Aryan-Kodan/Multi_Channel_DSO/images/KiCad/PCB.png

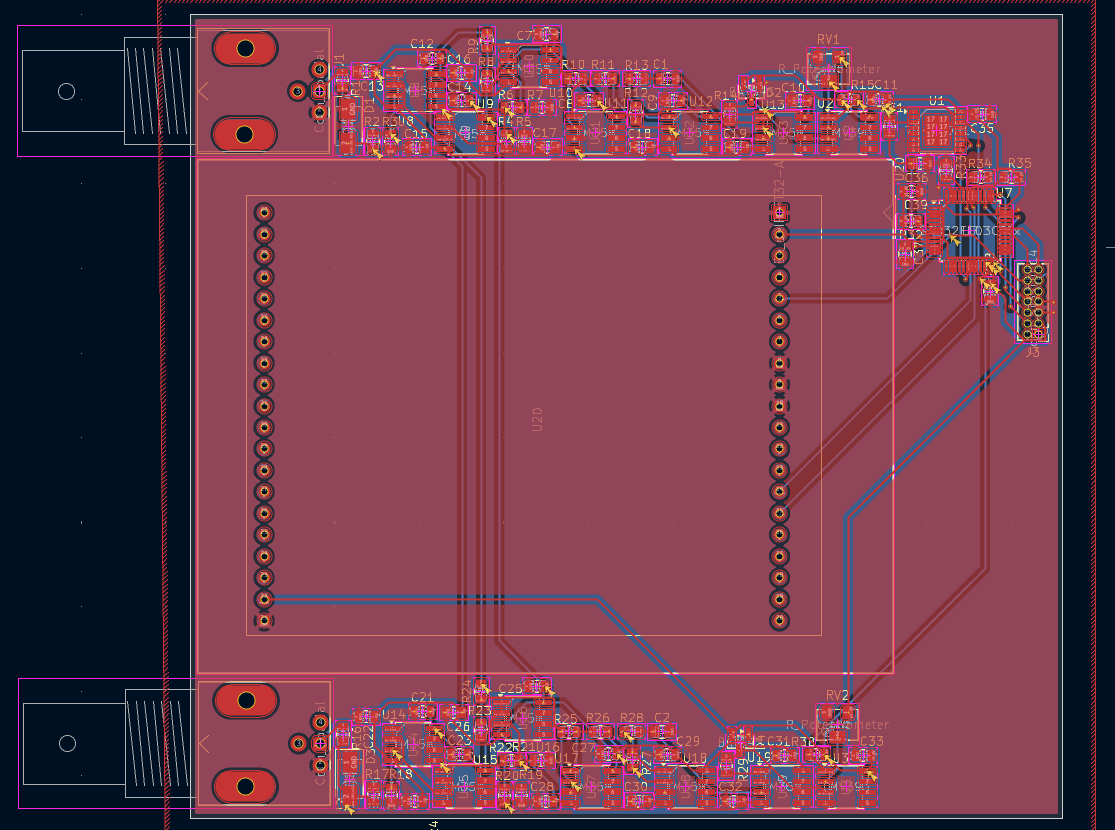
images/KiCad/PCB.png
