Aryan-Kodan/Multi_Channel_DSO/images/KiCad/PCB_3D.png

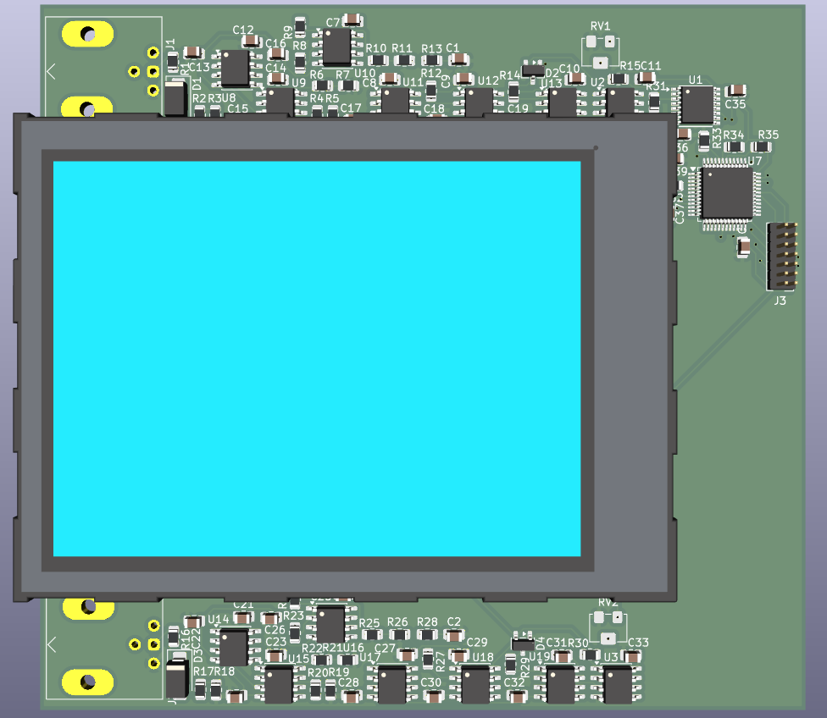
images/KiCad/PCB_3D.png
