Aryan-Kodan/Multi_Channel_DSO/images/LTspice/Input_waveform.png

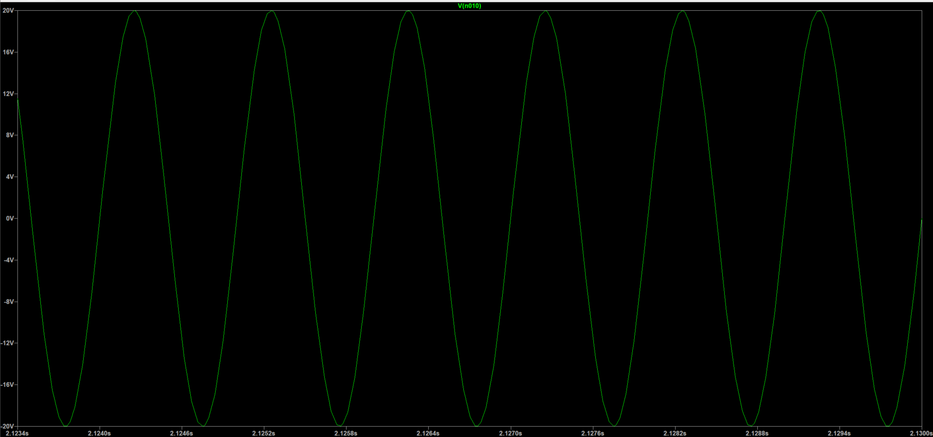
images/LTspice/Input_waveform.png
