Aryan-Kodan/Multi_Channel_DSO/LTspice/Osc_front.asc

C1: cap; 100n
C2: cap; 100n
C3: cap; 100n
C4: cap; 100n
C5: cap; 100n
C6: cap; 100n
C7: cap; 100n
C8: cap; 100n
C9: cap; 100n
C10: cap; 100n
C11: cap; 1n
C12: cap; 100n
C13: cap; 100n
D1: TVSdiode; SMBJ24CA
D2: schottky; BAT54
D3: schottky; BAT54
R1: res; 100; tol=1 pwr=0.1
R2: res; 900k
R3: res; 100k
R4: res; 10k
R5: res; 10k
R6: res; 15k
R7: res; 10k
R8: res; 10k
R9: res; 10k
R10: res; 10k
R11: res; 10k
R12: res; 10k
R13: res; 1.6k
R14: res; 47
U1: UniversalOpAmp
U2: UniversalOpAmp
U3: UniversalOpAmp
U4: UniversalOpAmp
U5: UniversalOpAmp
U6: UniversalOpAmp
V1: voltage; SINE(0 40 1k); AC 1
V2: voltage; 5
V3: voltage; -5
V4: voltage; 1.65
V5: voltage; 3.3
Named nets: 0, +5v, -5V, 1.65V, Output, 3.3V
;.ac dec 100 10 10mega
.tran 10
